mikey60/ESP32-Energy-Monitor/Data/energy meter.cir

[Main]
FileType=CIR
Version=12.00
Program=Micro-Cap
Component Version=10.00
Shape Version=11.00
Screen=1920,1080
MCAPVersion=12.2.0.3
Key ID=Demo
NLCnt=148
TXCnt=1

[shapedef]
Name=Capacitor
Line=0,0,22,0
Line=22,-8,22,8
Line=26,-8,26,8
Line=26,0,48,0
Current=32,12,16,12

[shapedef]
Name=Diode
Root="Diode.root",0,0,0

[shapedef]
Name=Diode.root
Line=0,0,20,0
Line=28,0,48,0
Rectangle=18,-8,20,8
PolyClosed=3
PolyLine=20,0
PolyLine=28,-8
PolyLine=28,8
Current=32,16,16,16

[shapedef]
Name=Ground
Line=0,0,12,0
Line=12,-8,12,8
Line=18,-4,18,4
Line=24,0,24,0

[shapedef]
Name=LoopGain
Line=0,0,48,0
PolyClosed=3
PolyLine=13,-3
PolyLine=13,3
PolyLine=16,0
PolyClosed=3
PolyLine=32,-3
PolyLine=32,3
PolyLine=35,0
Line=30,-6,18,6
Line=18,-6,30,6

[shapedef]
Name=Minus.root
Line=-2,0,2,0

[shapedef]
Name=Opamp5
Root="Opamp.root",0,0,0
Root="Plus.root",25,-4,0
Root="Minus.root",25,52,0
Line=32,56,32,34
Line=32,-8,32,13

[shapedef]
Name=Opamp.root
Line=0,48,6,48
Line=0,0,5,0
Line=6,-4,6,52
Line=6,-4,48,24
Line=6,52,48,24
Line=48,24,72,24
Line=10,12,14,12
Line=12,10,12,14
Line=10,36,14,36
Line=4,0,6,0

[shapedef]
Name=Plus.root
Line=-2,0,2,0
Line=0,-2,0,2

[shapedef]
Name=Regulator
Rectangle=16,-8,48,24
FColor=None
PolyClosed=3
PolyLine=32,6
PolyLine=24,14
PolyLine=40,14
Rectangle=24,4,40,6
Rectangle=23,2,24,6
Rectangle=40,4,41,8
Line=32,-16,32,4
Line=32,14,32,32
Line=30,8,8,8

[shapedef]
Name=Resistor
PolyOpen=12
PolyLine=0,0
PolyLine=0,0
PolyLine=12,0
PolyLine=14,-4
PolyLine=18,4
PolyLine=22,-4
PolyLine=26,4
PolyLine=30,-4
PolyLine=34,4
PolyLine=36,0
PolyLine=48,0
PolyLine=48,0
Current=32,8,16,8

[shapedef]
Name=SPICE_V
Root="Vsource.root",0,0,0

[shapedef]
Name=Vsource.root
Line=0,0,12,0
Line=36,0,48,0
Ellipse=12,-12,36,12
FColor=None
Line=7,5,7,9
Root="Plus.root",41,7,0
Current=32,16,16,16

[compdef]
Name=LMC6484_NS
Definition=Subckt
Shape=Opamp5
Mask=4224
Used=10
memo=CMOS Quad Rail to Rail Input and Output Opamp
Label Offset=51,34,-8,44
PinCnt=5
Pin="1",a,0,0,-3,-4
Pin="2",a,0,6,-3,18
Pin="99",a,4,-1,6,15
Pin="50",a,4,7,6,0
Pin="40",a,9,3,-3,-3

[compdef]
Name=Resistor
Definition=Resistor
Shape=Resistor
Mask=6401
Used=183
memo=Resistor
Label Offset=18,6,8,11
PinCnt=2
Pin="Plus",6,0,-10,-4
Pin="Minus",0,0,-14,-4

[compdef]
Name=Ground
Definition=Ground
Shape=Ground
Mask=1793
Used=268
memo=Ground
Label Offset=0,0,0,0
PinCnt=1
Pin="PinA",0,0,-3,-7

[compdef]
Name=Voltage Source
Definition=VSpice
Shape=SPICE_V
Mask=4865
Used=46
memo=Voltage Source
Label Offset=19,13,15,13
PinCnt=2
Pin="Plus",6,0,-5,-6
Pin="Minus",0,0,-20,-6

[compdef]
Name=Capacitor
Definition=Capacitor
Shape=Capacitor
Mask=7425
Used=39
memo=Capacitor
Label Offset=16,12,12,12
PinCnt=2
Pin="Plus",6,0,-3,-5
Pin="Minus",0,0,-14,-5

[compdef]
Name=ncp1117_33-x
Definition=Subckt
Shape=Regulator
Mask=4224
Used=2
memo=On Semi
Label Offset=51,-5,-14,49
PinCnt=3
Pin="1",a,1,1,-2,-3
Pin="2",a,4,4,5,4
Pin="3",a,4,-2,5,8

[compdef]
Name=1N4001
Definition=Diode
Shape=Diode
Mask=4224
Used=4
memo=General Purpose Rectifier Vr=50V Io=1A
Label Offset=18,10,12,12
PinCnt=2
Pin="Anode",6,0,-13,-8
Pin="Cathode",0,0,-27,-8

[compdef]
Name=Loop Gain Probe
Definition=Loop Gain Probe
Shape=LoopGain
Mask=4096
Used=9
memo=This probe is used to designate the point to break the loop for a Stability analysis
Label Offset=12,8,10,9
PinCnt=2
Pin="Plus",0,0,-11,-1
Pin="Minus",6,0,-8,-1

[Circuit]
Window Placement=2,3, -1,-1, -8,-31, 0,0,1006,492
Default Object=Color=#000080
Default Object Font=Height=-15,FStyle=0,Color=#000080,Name=Arial
Default Object Apply Border To Text=No
Default Object Apply Fill To Text=No
Default Object GridSnap=No
NodeVoltageFormat=3
CurrentFormat=3
PowerFormat=3
PathDelayFormat=3
WarningFormat=3
GridTextFormulaFormat=3
Window Placement in Transient Analysis=0,1, -1,-1, -8,-31, 8,0,1339,680
Window Placement in AC Analysis=0,1, -1,-1, -8,-31, 130,130,1362,602
Window Placement in DC Analysis=2,3, -1,-1, -8,-31, 208,208,1440,680
Window Placement in HmDistortion Analysis=0,1, 0,804, -8,-31, 0,0,1006,492
Window Placement in Stability Analysis=2,3, -1,-1, -8,-31, 55,50,1287,522
SpiceType=AMBIGUOUS
Title_Block_Border=None
Title_Block=False
Show Nodes=False
Show Voltages=False
Show Current=False
Show Power=False
Show Condition=False
Show Pin Connections=False
Show Connection Warnings=False
Show Cross=False
Show Attribute Text=True
Show Grid Text=True

[Comp]
Name=LMC6484_NS
Px=800,368

[Attr]
ON=6,60,PART
V=X2
Style=8192

[Attr]
ON=37,47,NAME
V=LMC6484_NS
Style=8192

[Attr]
ON=51,76,PACKAGE
V=DIP14

[Attr]
ON=51,90,GATE
V=A

[Attr]
ON=51,104,COMPNAME
V=UX1

[Comp]
Name=Resistor
Px=680,184
Rot=1

[Attr]
ON=8,11,PART
V=R1
Style=8192

[Attr]
ON=8,25,RESISTANCE
V=22K
Style=8192

[Attr]
ON=0,0,PACKAGE
V

[Comp]
Name=Resistor
Px=680,104
Rot=1

[Attr]
ON=8,11,PART
V=R2
Style=8192

[Attr]
ON=8,25,RESISTANCE
V=22K
Style=8192

[Attr]
ON=0,0,PACKAGE
V

[Comp]
Name=Resistor
Px=800,296

[Attr]
ON=20,9,PART
V=R3
Style=8192

[Attr]
ON=21,-18,RESISTANCE
V=10k
Style=8192

[Attr]
ON=0,0,PACKAGE
V

[Wire]
Pxs=680,176,720,176

[Wire]
Pxs=680,152,680,176

[Wire]
Pxs=680,176,680,184

[Wire]
Pxs=848,296,920,296

[Wire]
Pxs=744,296,800,296

[Comp]
Name=Resistor
Px=464,200

[Attr]
ON=21,6,PART
V=R4
Style=8192

[Attr]
ON=21,-18,RESISTANCE
V=75K
Style=8192

[Attr]
ON=0,0,PACKAGE
V

[Comp]
Name=Resistor
Px=680,416

[Attr]
ON=17,18,PART
V=R5
Style=8192

[Attr]
ON=12,-23,RESISTANCE
V=75K
Style=8192

[Attr]
ON=0,0,PACKAGE
V

[Comp]
Name=Resistor
Color=#000000
FColor=#000000
Px=880,336
Rot=2

[Attr]
ON=-27,-20,PART
V=R6
Style=8192
Color=#000000

[Attr]
ON=-32,13,RESISTANCE
V=5.6K
Style=8192
Color=#000000

[Attr]
ON=0,0,FREQ
V
Color=#000000

[Attr]
ON=0,0,MODEL
V
Color=#000000

[Attr]
ON=0,0,SMOKE
V
Color=#000000

[Attr]
ON=0,0,FSV
V
Color=#000000

[Attr]
ON=0,0,COST
V
Color=#000000

[Attr]
ON=0,0,POWER
V
Color=#000000

[Attr]
ON=0,0,PACKAGE
V
Color=#000000

[Wire]
Pxs=696,320,696,368

[Wire]
Pxs=696,368,744,368

[Comp]
Name=Ground
Px=680,248
Rot=7

[Comp]
Name=Ground
Px=824,232
Rot=7

[Comp]
Name=Ground
Px=832,424
Rot=7

[Wire]
Pxs=680,232,680,248

[Comp]
Name=Resistor
Color=#000000
FColor=#000000
Px=808,472

[Attr]
ON=8,11,PART
V=R7
Style=8192
Color=#000000

[Attr]
ON=8,-20,RESISTANCE
V=5.6K
Style=8192
Color=#000000

[Attr]
ON=0,0,FREQ
V
Color=#000000

[Attr]
ON=0,0,MODEL
V
Color=#000000

[Attr]
ON=0,0,SMOKE
V
Color=#000000

[Attr]
ON=0,0,FSV
V
Color=#000000

[Attr]
ON=0,0,COST
V
Color=#000000

[Attr]
ON=0,0,POWER
V
Color=#000000

[Attr]
ON=0,0,PACKAGE
V
Color=#000000

[Wire]
Pxs=976,392,976,472

[Wire]
Pxs=856,472,976,472

[Wire]
Pxs=728,472,808,472

[Comp]
Name=Resistor
Px=656,560
Rot=1

[Attr]
ON=8,11,PART
V=R8
Style=8192

[Attr]
ON=8,25,RESISTANCE
V=56
Style=8192

[Attr]
ON=0,0,PACKAGE
V

[Comp]
Name=Resistor
Px=752,560
Rot=1

[Attr]
ON=8,11,PART
V=R9
Style=8192

[Attr]
ON=8,25,RESISTANCE
V=56
Style=8192

[Attr]
ON=0,0,PACKAGE
V

[Wire]
Pxs=656,544,656,560

[Wire]
Pxs=656,544,752,544

[Wire]
Pxs=752,544,752,560

[Wire]
Pxs=752,544,920,544

[Wire]
Pxs=752,608,752,680

[Wire]
Pxs=656,608,656,648

[Comp]
Name=Voltage Source
Px=80,408
Rot=3

[Attr]
ON=-31,-27,PART
V=V1
Style=8192

[Attr]
ON=-80,-41,VALUE
V=DC 0 AC 1 0 Sin 0 11.8 60 0 0 0

[Attr]
ON=0,0,PACKAGE
V

[Attr]
ON=0,0,SMOOTHING
V=N
Style=256

[Attr]
ON=0,0,Saved_PulseS
V=N
Style=256

[Attr]
ON=0,0,FRACTION
V=.2
Style=256

[Attr]
ON=0,0,Saved_PulseF
V=.2
Style=256

[Attr]
ON=0,0,Saved_Pulse
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
Style=8192

[Attr]
ON=0,0,PACKAGE
V

[Wire]
Pxs=456,488,496,488

[Wire]
Pxs=456,264,456,440

[Comp]
Name=Capacitor
Px=720,240
Rot=5

[Attr]
ON=9,-32,PART
V=C4
Style=8192

[Attr]
ON=9,-48,CAPACITANCE
V=1uF
Style=8192

[Attr]
ON=0,0,PACKAGE
V

[Wire]
Pxs=720,176,720,192

[Wire]
Pxs=720,176,792,176

[Wire]
Pxs=720,240,720,248

[Wire]
Pxs=680,248,720,248

[Comp]
Name=1N4001
Px=400,232
Rot=2

[Attr]
ON=18,10,PART
V=D7
Style=8192

[Attr]
ON=18,24,MODEL
V=1N4001

[Attr]
ON=18,52,PACKAGE
V=DO-41

[Comp]
Name=1N4001
Px=448,232
Rot=2

[Attr]
ON=18,10,PART
V=D8
Style=8192

[Attr]
ON=18,24,MODEL
V=1N4001

[Attr]
ON=18,52,PACKAGE
V=DO-41

[Wire]
Pxs=296,232,352,232

[Wire]
Pxs=296,232,296,264

[Wire]
Pxs=400,232,416,232

[Wire]
Pxs=448,232,496,232

[Wire]
Pxs=496,232,496,264

[Comp]
Name=Loop Gain Probe
Px=928,392

[Attr]
ON=12,8,PART
V=Probe1
Style=8192

[Attr]
ON=0,0,PACKAGE
V

[Comp]
Name=Ground
Px=592,128
Rot=7

[Wire]
Pxs=632,80,632,344

[Comp]
Name=Capacitor
Px=1032,304
Rot=5

[Attr]
ON=12,-26,PART
V=C7
Style=8192

[Attr]
ON=12,-49,CAPACITANCE
V=120pf
Style=8192

[Attr]
ON=0,0,PACKAGE
V

[Wire]
Pxs=920,256,1032,256

[Wire]
Pxs=864,200,872,200

[Wire]
Pxs=528,488,568,488

[Wire]
Pxs=528,352,528,440

[Wire]
Pxs=520,352,528,352

[Comp]
Name=LMC6484_NS
Px=792,176

[Attr]
ON=51,34,PART
V=X5
Style=8192

[Attr]
ON=44,-15,NAME
V=LMC6484_NS
Style=8192

[Attr]
ON=51,76,PACKAGE
V=DIP14

[Attr]
ON=51,90,GATE
V=A

[Attr]
ON=51,104,COMPNAME
V=UX1

[Wire]
Pxs=744,224,744,264

[Comp]
Name=Voltage Source
Px=592,128
Rot=3

[Attr]
ON=-31,-27,PART
V=V5
Style=8192

[Attr]
ON=-80,-41,VALUE
V=DC 3.3 AC 1 0

[Attr]
ON=0,0,PACKAGE
V

[Attr]
ON=0,0,SMOOTHING
V=N
Style=256

[Attr]
ON=0,0,Saved_PulseS
V=N
Style=256

[Attr]
ON=0,0,FRACTION
V=.2
Style=256

[Attr]
ON=0,0,Saved_PulseF
V=.2
Style=256

[Attr]
ON=0,0,Saved_Pulse
V=DC 0 AC 1 0 Pulse 0 5 100n 10n 10n 400n 1u
Style=256

[Attr]
ON=0,0,Saved_Sin
V=DC 3.3 AC 1 0 Sin 0 1 60 0 0 0
Style=256

[Attr]
ON=0,11,Saved_None
V=DC 3.3 AC 1 0
Style=256

[Wire]
Pxs=512,200,648,200

[Wire]
Pxs=920,256,920,296

[Wire]
Pxs=728,416,728,472

[Wire]
Pxs=728,416,800,416

[Wire]
Pxs=952,392,976,392

[Wire]
Pxs=872,392,928,392

[Wire]
Pxs=976,392,1112,392

[Comp]
Name=Ground
Px=1032,304
Rot=7

[Wire]
Pxs=920,336,920,544

[Wire]
Pxs=744,336,744,368

[Wire]
Pxs=632,80,680,80

[Wire]
Pxs=632,344,832,344

[Wire]
Pxs=592,80,632,80

[Wire]
Pxs=208,200,464,200

[Comp]
Name=Loop Gain Probe
Px=744,224

[Attr]
ON=12,8,PART
V=Probe2
Style=8192

[Attr]
ON=0,0,PACKAGE
V

[Wire]
Pxs=776,248,792,248

[Comp]
Name=Capacitor
Px=808,264
Rot=6

[Attr]
ON=-61,-15,PART
V=C8
Style=8192

[Attr]
ON=-50,12,CAPACITANCE
V=200pF
Style=8192

[Attr]
ON=0,0,PACKAGE
V

[Comp]
Name=Resistor
Px=920,200
Rot=1

[Attr]
ON=8,11,PART
V=R19
Style=8192

[Attr]
ON=8,25,RESISTANCE
V=100
Style=8192

[Attr]
ON=0,0,PACKAGE
V

[Wire]
Pxs=744,264,760,264

[Wire]
Pxs=744,264,744,296

[Wire]
Pxs=808,264,872,264

[Wire]
Pxs=872,200,872,264

[Wire]
Pxs=872,200,920,200

[Wire]
Pxs=920,248,920,256

[Grid Text]
Text="Transformer Secondary"
Text="Resistance"
Px=56,328
GridSnap=True
JustifyH=Left
JustifyV=Bottom
CBorder=None

[Schematic]
CurrentSection 0=0
CurrentSection 1=0
CurrentSection 2=0
CurrentSection 3=0
Splitter.xs=0
Splitter.ys=0
TextQuad=4099
Scale=1
GridUser=10
ShapeGroups="Main","Euro","Polarity","Main1","Main11","Electrolytic","GroundArrow","DeMorgan"
CalcRMS=False
CalcAVG=False
CalcPeak=False
CalcVoltage=True
DisplayMeasure=Last
ShareScales=True

[Tools]
Pos=Top
FILESAVEASOLD=No
BOM=No
FILEPCB=No
PROBE=Yes
SELECT=Yes
PAN=Yes
COMP=Yes
TEXT=Yes
WIRE=Yes
WIRED=Yes
BUS=Yes
GRAPHIC=Yes
FLOWCHART=Yes
LINE=No
ELLIPSE=No
RECT=No
DIAM=No
ARC=No
PIE=No
TRIANGLE=No
STAR=No
LEFTBRK=No
RIGHTBRK=No
BOTHBRK=No
META=Yes
PARALLELOGRAM=No
FC_PROCESS=No
FC_ALT_PROCESS=No
FC_DECISION=No
FC_DATA=No
FC_PREDEFPROCESS=No
FC_INTERNALSTORAGE=No
FC_DOCUMENT=No
FC_MULTIDOCUMENT=No
FC_TERMINATOR=No
FC_PREPARATION=No
FC_MANUALINPUT=No
FC_MANUALOPERATION=No
FC_CONNECTOR=No
FC_OFFPAGECONNECTOR=No
FC_PUNCHCARD=No
FC_PUNCHEDTAPE=No
FC_SUMMING_JUNCTION=No
FC_OR=No
FC_COLLATE=No
FC_SORT=No
FC_EXTRACT=No
FC_MERGE=No
FC_STORED_DATA=No
FC_DELAY=No
FC_SAS=No
FC_MAGNETIC_DISK=No
FC_DAS=No
FC_DISPLAY=No
SPREAD_SHEET=Yes
POLYCLOS=No
POLYOPEN=No
FLAG=Yes
INFO=Yes
HELP=Yes
HELP_SPICE=No
LINK=Yes
CHECK=Yes
REGION_ENABLE=Yes
TITLE_BLOCK=Yes
DIGTRC=No
DIGTRC2=No
BUILD_COMMAND=Yes
DIGALL=No
GRIDTEXT=Yes
COMPTEXT=Yes
NODE=Yes
MEASURED=Yes
NODEV=Yes
CURRENT=Yes
POWER=Yes
CONDITIN=Yes
PIN=Yes
CONNWARN=Yes
CROSS=Yes
GRID=Yes
BORDER=Yes
BORDERONE=Yes
TITLE=Yes
RUBBER=Yes
PROPERTY=Yes
STEP=Yes
MIRROR=Yes
ROTATE=Yes
FLIPY=Yes
FLIPX=Yes
CIR_MAKEMACRO=No
CLEARCUTWIRE=No
CLIPBOARDCIRPAGE2BMM=No
FINDCOMP=Yes
FIND=Yes
REPEAT=No
REPLACE=No
MODEL=Yes
CIR2CKT=Yes
ATTDISP=Yes
ENABLE=Yes
DISABLE=Yes
ENABLE_WITH=Yes
TOFRONT=Yes
TOBACK=Yes
SELNEXT=Yes
PAGEADD=Yes
PAGEADDTEXT=No
ADDSECTION=No
PAGEDEL=Yes
ZOOMIN=Yes
ZOOMOUT=Yes
AUTOSCALECIR=Yes
GOTOFLAG=Yes
UPLEVEL=Yes
COLOR=Yes
FONT=Yes
STYLE=Yes
DM_LAST=No
DM_RMS=No
DM_AVG=No
DM_PEAK=No
GRID_NONE=No
GRID_NORMAL=No
GRID_BOLD_5=No
GRID_BOLD_6=No
GRID_BOLD_USER=No
GRAPH_PAPER=No
SPLITCIRTEXTH=No
SPLITCIRTEXTV=No
SPACE_SPLITTERS_EVENLY=No
NORMALCIR=No
RENAMEDEFINE=No
RENAMECMP=No
ATTALIGN=No
RESETNODEPOS=No
FIT2STANDARD=No
NODESNAP=No
MOVETEXT=No
TEXTINC=No
TOGGLETEXT=No
TOGGLEMODE=No
TOLERANCE=No
ALIGNAB=No
ALIGNLEFT=Yes
ALIGNCENTER=Yes
ALIGNRIGHT=Yes
ALIGNTOP=Yes
ALIGNMIDDLES=Yes
ALIGNBOTTOM=Yes

[Section]
Index=0
Name="energy meter"
Type=Main
Enable=True
CurrentPage 0=0
CurrentPage 1=0
CurrentPage 2=0
CurrentPage 3=0
TabSize 0=425
TabSize 1=425
TabSize 2=425
TabSize 3=425

[Page]
Index=0
Section=0
Print=True
Enable=True
Name=Main
PrinterScale=1
Scale 0=1
Scale 1=1
Scale 2=1
SB 3=0,97
Scale 3=1
Px=845,617
WinBackGround Color=#FFFFFF
Select Color=#FF0000
Anchor Color=#000000
Select Box Color=#000080
Grid Text Color=Height=-12,FStyle=0,Color=#0000FF,Name=Verdana
Grid Text RTF=False
Grid Text Angle=0
Grid Text GridSnap=True
Grid Text PinIt=False
Grid Text JustifyH=Left
Grid Text JustifyV=Bottom
Grid GradientColor2=None
Grid OutlineThickness=1
Grid OutlineColor=None
Component Color=#0000FF
Attribute Text=Height=-12,FStyle=0,Color=#008000,Name=Verdana
Wire Color=#008000
Bus Color=#008000
Pin Connection=Height=-10,FStyle=0,Color=#FF0000,Name=Arial
Pin Marker Color=#008000
Node Number=Height=-11,FStyle=0,Color=#FF00FF,Name=Arial
Node Voltage Color=Height=-11,FStyle=0,Color=#000000,Name=Arial
Dynamic AC Voltage Color=#E4E4E4
Text Banner Text=Height=-15,FStyle=0,Color=#800000,Name=Arial
Title Block Background=#C0C0C0
Current=Height=-11,FStyle=0,Color=#0000FF,Name=Arial
Power/Condition=Height=-11,FStyle=0,Color=#FF0000,Name=Arial
Digital Path Color=#FF0000
Title Block Border=#000000
Disabled	Color=#C0C0C0
Search Color=#FFFF00
Grid Color=#000000
Graph Paper=#E4E4E4
Digital 0 Color=#000000
Digital R Color=#FFFF00
Digital F Color=#FFFF00
Digital 1 Color=#FF0000
Digital X Color=#C0C0C0
Digital Z Color=#808080
Block Select Color=#51F998

[Page]
Index=1
Section=0
Type=Text
Print=False
Enable=True
Name=Text
Font=Height=-15,FStyle=0,Color=#000000,Name=Courier New
Comment Color=#008000
WinBackGround Color=#FFFFFF
Disabled	Color=#C0C0C0
KeyWord Color=#0000FF
Error	Color=#FF0000
Search Color=#FFFF00

[Page]
Index=2
Section=0
Type=Text
Print=False
Enable=True
Name=Models
Font=Height=-15,FStyle=0,Color=#000000,Name=Courier New
Comment Color=#008000
WinBackGround Color=#FFFFFF
Disabled	Color=#C0C0C0
KeyWord Color=#0000FF
Error	Color=#FF0000
Search Color=#FFFF00

[Page]
Index=3
Section=0
Type=Info
Print=False
Enable=True
Name=Info
Font=Height=-15,FStyle=0,Color=#000000,Name=Courier New
Comment Color=#008000
WinBackGround Color=#FFFFFF
Disabled	Color=#C0C0C0
KeyWord Color=#0000FF
Error	Color=#FF0000
Search Color=#FFFF00

[Text Area]
Section=0
Page=1
Text=.OPTIONS ITL1=250
Text=.OPTIONS PIVREL=1

[Text Area]
Section=0
Page=2

[InfoPage]
InfoPage=True
Warnings=True
System=True
Defines=True
Array=True
Model=True
Measure=True
MacroSubckt=True
NotUsed=True
ComponentCounts=True
VariablizePaths=False
DontShowPaths=False
SimulationLog=True

[Transient]
WinID=1
Window Placement=0,1, -1,-1, -8,-31, 215,89,1221,581
Font=Height=-19,FStyle=0,Color=#0000FF,Name=Arial
WinBackGround Color=#FFFFFF
Select Color=#FF0000
Anchor Color=#000000
Select Box Color=#000080
Title=energy meter.cir
AutoTitle=Yes
Grid Color=#808080
Grid Weight=1
Grid Pattern=Dot6
Tracker Foreground=Height=-15,FStyle=0,Color=#000000,Name=Arial
Tracker Background=#FFFF00
Baseline color=#0000FF
BaseLine Weight=1
CurveFit color=#FF0000
CurveFit Weight=2
CurveFit Pattern=Dash
Static Grids=False
PlusMark=False
MinorLog25=Off
LabelMinor=Off
DataPoints=False
Token=False
Ruler=False
XAxisGrids=True
YAxisGrids=True
MinorLogGrids=True
BaseLine=False
AlignZ=True
Align Cursors=True
TagFormatX=3
TagFormatY=3
FormulaFormat=2
EndMode=SCALE
Graph Background=#FFFFFF
Tracker Intercept=False
Tracker Mouse=True
Tracker Cursor=True
Tracker Cursor BranchInfo=False
Horizontal Cursor=False
Same Y Scales=Yes
Enable X Scaling=True
Enable Y Scaling=True
Keep X Scales The Same=True
Number of Grids X=5
Number of Grids Y=5
Cursor Select Color Primary=#C0C0C0
Cursor Select Color Secondary=#FF0000
Data Point Labels Color Fore=Height=-15,FStyle=0,Color=#000000,Name=Arial
Data Point Labels Color Back=#FFFF00
OperPoint=True
OperPointOnly=False
AutoScaleRanges=True
FixedTimeStep=False
DoPSS=False
PSS_Periods="1"
PSS_Iterations="5"
PSS_Error="1u"
PSS_ShowPlots=True
FFT_NPts="8192"
FFT_IncludeDCHarmonic=False
FFT_AutoScale_Harmonics="10"
PrinterAutoTile=No
PrinterBlackBorder=No
MonMaxShow=12
MonPageWidth=66
MonPlotWidth=21
MonExprXWidth=142
MonExprYWidth=367
MonRangeXWidth=90
MonRangeYWidth=90
AnimateWait=None
AnimateWaitTime=500
AnimatePressAfter=0
Save_For_Future=No
Reduce_Display=1
Reduce_Save=1
Reduce_ThrowDataOut=0
Num Out Header Left
Num Out Header Center="$MC\n$user\n$company\n$Analysis of $name\n$date $time"
Num Out Header Right
Num Out Delimiter=32
Num Out Write=True
Num Out Write Main Header=True
Num Out Write Limits=True
Num Out Write Branch Header=True
Num Out Write Models=False
Num Out Write Zero Models=True
Num Out Write Undefined Models=True
Num Out Write Operating Point=True
Num Out Write Measurement Values=True
Num Out Write Tolerance Detail=True
Num Out Write Values=True
Num Out Write Waveform Header=True
Num Out Allow Dup Y Expr=False
Num Out Low="TSTART"
Num Out High="TMAX"
Num Out Font=Height=-15,FStyle=0,Color=#000000,Name=Courier New
Num Out Format=3
Num Out HideNonSelected=False
Num Out UseActualDataPoints=False
AutoSaveWave=False
Wave Format=16E
State Variables Format=5E
Print Individual Pages=False

[Tools]
Pos=Top
SELECT=Yes
PAN=Yes
GRAPHIC=Yes
LINE=No
ELLIPSE=No
RECT=No
DIAM=No
ARC=No
PIE=No
TRIANGLE=No
STAR=No
LEFTBRK=No
RIGHTBRK=No
BOTHBRK=No
META=Yes
PARALLELOGRAM=No
POLYCLOS=No
POLYOPEN=No
SCALE=Yes
CURSOR=Yes
MEASUREH=Yes
MEASUREV=Yes
TAG=Yes
PTAG=Yes
TEXT=Yes
PROPERTY=Yes
START=Yes
STOP=Yes
PAUSE=Yes
RESUME=No
DATAPTS=Yes
TOKENS=Yes
RULER=Yes
PLUS=Yes
XAXIS=Yes
YAXIS=Yes
MINORLOG=Yes
LOG25=Yes
BASELINE=Yes
HORIZCUR=Yes
GOTOX=Yes
GOTOY=Yes
GOTOPERF=Yes
GOTOBRNC=Yes
CLEAR_ACCUMULATED=Yes
PDELETE_ALL_PLOTS=Yes
NEXT=Yes
NEXTIN=Yes
PEAK=Yes
VALLEY=Yes
HIGH=Yes
LOW=Yes
INFLECTN=Yes
GHIGH=Yes
GLOW=Yes
BOTTOM=Yes
TOP=Yes
WAVEFORMBUFFER=Yes
AOUTPUT=Yes
PKEY=Yes
ENXSCALE=Yes
ENYSCALE=Yes
ZOOMIN=Yes
ZOOMOUT=Yes
AUTOSCALE=Yes
RESTORESCALE=No
COLOR=Yes
FONT=Yes
STYLE=Yes
SELNEXT=Yes
NORMALIZE=No
NORMALIZE_MIN=No
NORMALIZE_MAX=No
ADD_TAG_LEFT=No
ADD_TAG_RIGHT=No
ADD_HORZ_TAG=No
ADD_VERT_TAG=No
ALIGN_CURSORS=No
ALIGN_CURSORSZ=No
CURSORTOCLIPBOARD=No
TRACKER_CURSOR=No
TRACKER_CURSOR_BRANCHINFO=No
TRACKER_INTERCEPT=No
TRACKER_MOUSE=No
TOFRONT=Yes
TOBACK=Yes
SPLITCIRTEXTH=No
SPLITCIRTEXTV=No
SPACE_SPLITTERS_EVENLY=No
NORMALCIR=No
LABEL_WAVEFORM=No
LABEL_DATA_POINTS=No
WFB_ADD_TO_LIMITS=No
ENVELOPE=No
SAMEYSCALES=No
KEEPXSCALESTHESAME=No
CURVEFIT=No
ADD_MARKER=No
SHOWWATCH=No
BP=No
TOGGLEMODE=No
REMOVEALLTEXT=No
AUTOSCALEX=No
LABELALLMINOR=No
ALIGNLEFT=Yes
ALIGNCENTER=Yes
ALIGNRIGHT=Yes
ALIGNTOP=Yes
ALIGNMIDDLES=Yes
ALIGNBOTTOM=Yes

[APage]
Analysis=Transient
Name="MAIN"

[AC]
WinID=2
Window Placement=0,1, -1,-1, -8,-31, 130,130,1362,602
Font=Height=-19,FStyle=0,Color=#0000FF,Name=Arial
WinBackGround Color=#FFFFFF
Select Color=#FF0000
Anchor Color=#000000
Select Box Color=#000080
Title
AutoTitle=Yes
Grid Color=#808080
Grid Weight=1
Grid Pattern=Dot6
Tracker Foreground=Height=-15,FStyle=0,Color=#000000,Name=Arial
Tracker Background=#FFFF00
Baseline color=#0000FF
BaseLine Weight=1
CurveFit color=#FF0000
CurveFit Weight=2
CurveFit Pattern=Dash
Static Grids=False
PlusMark=False
MinorLog25=Off
LabelMinor=Off
DataPoints=False
Token=False
Ruler=False
XAxisGrids=True
YAxisGrids=True
MinorLogGrids=True
BaseLine=False
AlignZ=True
Align Cursors=True
TagFormatX=3
TagFormatY=3
FormulaFormat=2
EndMode=SCALE
Graph Background=#FFFFFF
Tracker Intercept=False
Tracker Mouse=True
Tracker Cursor=True
Tracker Cursor BranchInfo=False
Horizontal Cursor=False
Same Y Scales=Yes
Enable X Scaling=True
Enable Y Scaling=True
Keep X Scales The Same=True
Number of Grids X=5
Number of Grids Y=5
Cursor Select Color Primary=#C0C0C0
Cursor Select Color Secondary=#FF0000
Data Point Labels Color Fore=Height=-15,FStyle=0,Color=#000000,Name=Arial
Data Point Labels Color Back=#FFFF00
OperPoint=True
AutoScaleRanges=True
FFT_NPts="8192"
FFT_IncludeDCHarmonic=False
FFT_AutoScale_Harmonics="10"
PrinterAutoTile=No
PrinterBlackBorder=No
MonMaxShow=3
MonPageWidth=66
MonPlotWidth=21
MonExprXWidth=142
MonExprYWidth=260
MonRangeXWidth=90
MonRangeYWidth=90
AnimateWait=None
AnimateWaitTime=500
AnimatePressAfter=0
Save_For_Future=No
Reduce_Display=1
Reduce_Save=1
Reduce_ThrowDataOut=0
Num Out Header Left
Num Out Header Center="$MC\n$user\n$company\n$Analysis of $name\n$date $time"
Num Out Header Right
Num Out Delimiter=32
Num Out Write=True
Num Out Write Main Header=True
Num Out Write Limits=True
Num Out Write Branch Header=True
Num Out Write Models=False
Num Out Write Zero Models=True
Num Out Write Undefined Models=True
Num Out Write Operating Point=True
Num Out Write Measurement Values=True
Num Out Write Tolerance Detail=True
Num Out Write Noise=True
Num Out Write Values=True
Num Out Write Waveform Header=True
Num Out Allow Dup Y Expr=False
Num Out Low="FMIN"
Num Out High="FMAX"
Num Out Font=Height=-15,FStyle=0,Color=#000000,Name=Courier New
Num Out Format=3
Num Out HideNonSelected=False
Num Out UseActualDataPoints=False
AutoSaveWave=False
Wave Format=16E
State Variables Format=5E
Print Individual Pages=False

[Tools]
Pos=Top
SELECT=Yes
PAN=Yes
GRAPHIC=Yes
LINE=No
ELLIPSE=No
RECT=No
DIAM=No
ARC=No
PIE=No
TRIANGLE=No
STAR=No
LEFTBRK=No
RIGHTBRK=No
BOTHBRK=No
META=Yes
PARALLELOGRAM=No
POLYCLOS=No
POLYOPEN=No
SCALE=Yes
CURSOR=Yes
MEASUREH=Yes
MEASUREV=Yes
TAG=Yes
PTAG=Yes
TEXT=Yes
PROPERTY=Yes
START=Yes
STOP=Yes
PAUSE=Yes
RESUME=No
DATAPTS=Yes
TOKENS=Yes
RULER=Yes
PLUS=Yes
XAXIS=Yes
YAXIS=Yes
MINORLOG=Yes
LOG25=Yes
BASELINE=Yes
HORIZCUR=Yes
GOTOX=Yes
GOTOY=Yes
GOTOPERF=Yes
GOTOBRNC=Yes
CLEAR_ACCUMULATED=Yes
PDELETE_ALL_PLOTS=Yes
NEXT=Yes
NEXTIN=Yes
PEAK=Yes
VALLEY=Yes
HIGH=Yes
LOW=Yes
INFLECTN=Yes
GHIGH=Yes
GLOW=Yes
BOTTOM=Yes
TOP=Yes
WAVEFORMBUFFER=Yes
AOUTPUT=Yes
PKEY=Yes
ENXSCALE=Yes
ENYSCALE=Yes
ZOOMIN=Yes
ZOOMOUT=Yes
AUTOSCALE=Yes
RESTORESCALE=No
COLOR=Yes
FONT=Yes
STYLE=Yes
SELNEXT=Yes
NORMALIZE=No
NORMALIZE_MIN=No
NORMALIZE_MAX=No
ADD_TAG_LEFT=No
ADD_TAG_RIGHT=No
ADD_HORZ_TAG=No
ADD_VERT_TAG=No
ALIGN_CURSORS=No
ALIGN_CURSORSZ=No
CURSORTOCLIPBOARD=No
TRACKER_CURSOR=No
TRACKER_CURSOR_BRANCHINFO=No
TRACKER_INTERCEPT=No
TRACKER_MOUSE=No
TOFRONT=Yes
TOBACK=Yes
SPLITCIRTEXTH=No
SPLITCIRTEXTV=No
SPACE_SPLITTERS_EVENLY=No
NORMALCIR=No
LABEL_WAVEFORM=No
LABEL_DATA_POINTS=No
WFB_ADD_TO_LIMITS=No
ENVELOPE=No
SAMEYSCALES=No
KEEPXSCALESTHESAME=No
CURVEFIT=No
ADD_MARKER=No
SHOWWATCH=No
BP=No
TOGGLEMODE=No
REMOVEALLTEXT=No
AUTOSCALEX=No
LABELALLMINOR=No
ALIGNLEFT=Yes
ALIGNCENTER=Yes
ALIGNRIGHT=Yes
ALIGNTOP=Yes
ALIGNMIDDLES=Yes
ALIGNBOTTOM=Yes

[APage]
Analysis=AC
Name="MAIN"

[DC]
WinID=3
Window Placement=2,3, -1,-1, -8,-31, 208,208,1440,680
Font=Height=-19,FStyle=0,Color=#0000FF,Name=Arial
WinBackGround Color=#FFFFFF
Select Color=#FF0000
Anchor Color=#000000
Select Box Color=#000080
Title
AutoTitle=Yes
Grid Color=#808080
Grid Weight=1
Grid Pattern=Dot6
Tracker Foreground=Height=-15,FStyle=0,Color=#000000,Name=Arial
Tracker Background=#FFFF00
Baseline color=#0000FF
BaseLine Weight=1
CurveFit color=#FF0000
CurveFit Weight=2
CurveFit Pattern=Dash
Static Grids=False
PlusMark=False
MinorLog25=Off
LabelMinor=Off
DataPoints=False
Token=False
Ruler=False
XAxisGrids=True
YAxisGrids=True
MinorLogGrids=True
BaseLine=False
AlignZ=True
Align Cursors=True
TagFormatX=3
TagFormatY=3
FormulaFormat=2
EndMode=SCALE
Graph Background=#FFFFFF
Tracker Intercept=False
Tracker Mouse=True
Tracker Cursor=True
Tracker Cursor BranchInfo=False
Horizontal Cursor=False
Same Y Scales=Yes
Enable X Scaling=True
Enable Y Scaling=True
Keep X Scales The Same=True
Number of Grids X=5
Number of Grids Y=5
Cursor Select Color Primary=#C0C0C0
Cursor Select Color Secondary=#FF0000
Data Point Labels Color Fore=Height=-15,FStyle=0,Color=#000000,Name=Arial
Data Point Labels Color Back=#FFFF00
AutoScaleRanges=True
PrinterAutoTile=No
PrinterBlackBorder=No
MonMaxShow=3
MonPageWidth=66
MonPlotWidth=21
MonExprXWidth=142
MonExprYWidth=286
MonRangeXWidth=90
MonRangeYWidth=90
AnimateWait=None
AnimateWaitTime=500
AnimatePressAfter=0
Save_For_Future=No
Reduce_Display=1
Reduce_Save=1
Reduce_ThrowDataOut=0
Num Out Header Left
Num Out Header Center="$MC\n$user\n$company\n$Analysis of $name\n$date $time"
Num Out Header Right
Num Out Delimiter=32
Num Out Write=True
Num Out Write Main Header=True
Num Out Write Limits=True
Num Out Write Branch Header=True
Num Out Write Models=False
Num Out Write Zero Models=True
Num Out Write Undefined Models=True
Num Out Write Measurement Values=True
Num Out Write Tolerance Detail=True
Num Out Write Values=True
Num Out Write Waveform Header=True
Num Out Allow Dup Y Expr=False
Num Out Low="DCMIN"
Num Out High="DCMAX"
Num Out Font=Height=-15,FStyle=0,Color=#000000,Name=Courier New
Num Out Format=3
Num Out HideNonSelected=False
Num Out UseActualDataPoints=False
AutoSaveWave=False
Wave Format=16E
State Variables Format=5E
Print Individual Pages=False
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
